aqiuok/xiaozhi-smart-elf/photos/70CE8669092AEE571E4C6250777DF579.jpg

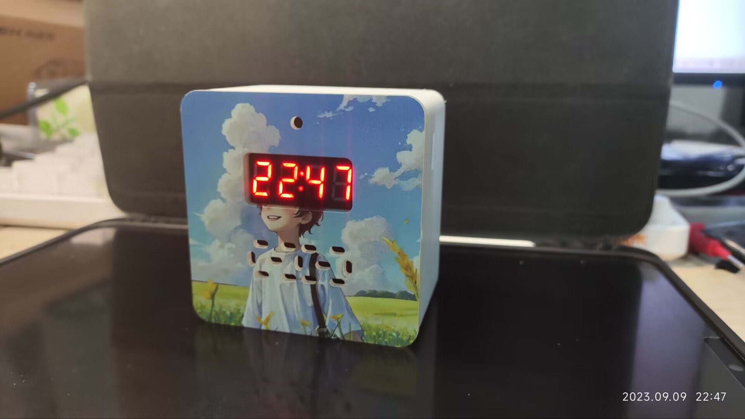
photos/70CE8669092AEE571E4C6250777DF579.jpg
