aqiuok/xiaozhi-smart-elf/photos/Bcm6qwBvF4b9TmoeZIAAMZd9puk0gAqJdHaOMHHB.jpeg

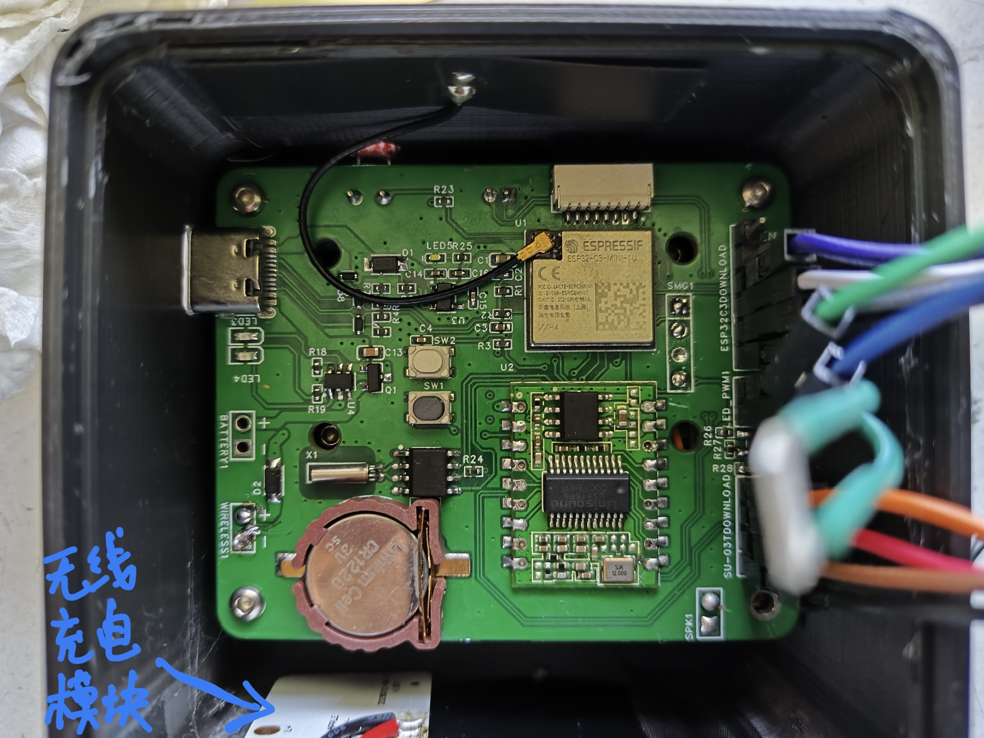
photos/Bcm6qwBvF4b9TmoeZIAAMZd9puk0gAqJdHaOMHHB.jpeg
