aqiuok/xiaozhi-smart-elf/photos/gcC11dQcpo1tZI9Yauk2vhwf6SmNw4uLY4zkg3At.png

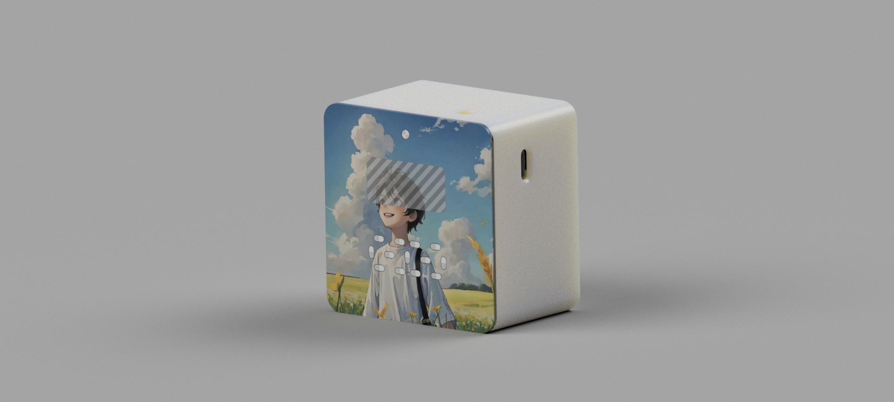
photos/gcC11dQcpo1tZI9Yauk2vhwf6SmNw4uLY4zkg3At.png
