aqiuok/xiaozhi-smart-elf/photos/QQ截图20240616194331.jpg

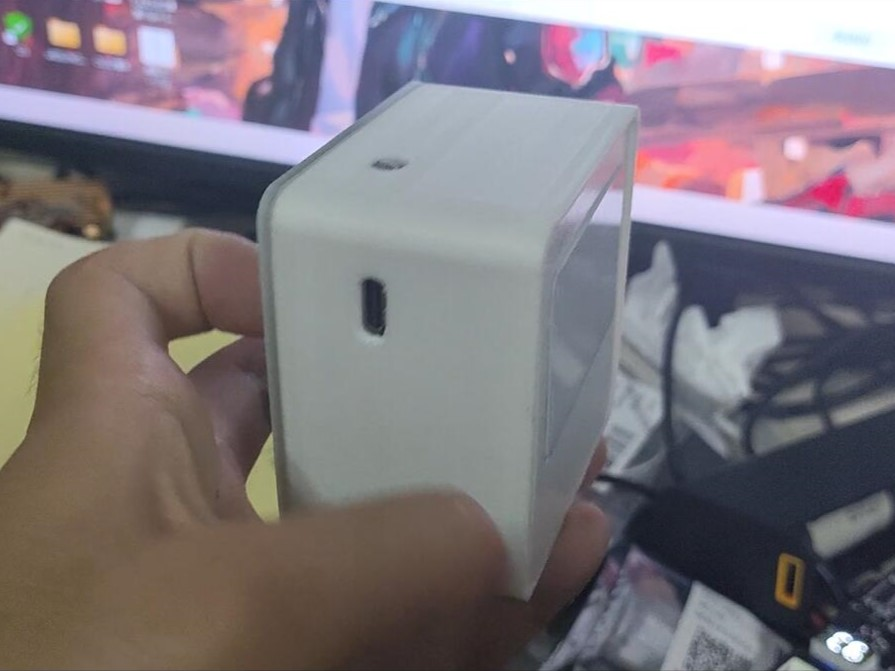
photos/QQ截图20240616194331.jpg
