aqiuok/xiaozhi-smart-elf/photos/前面.jpg

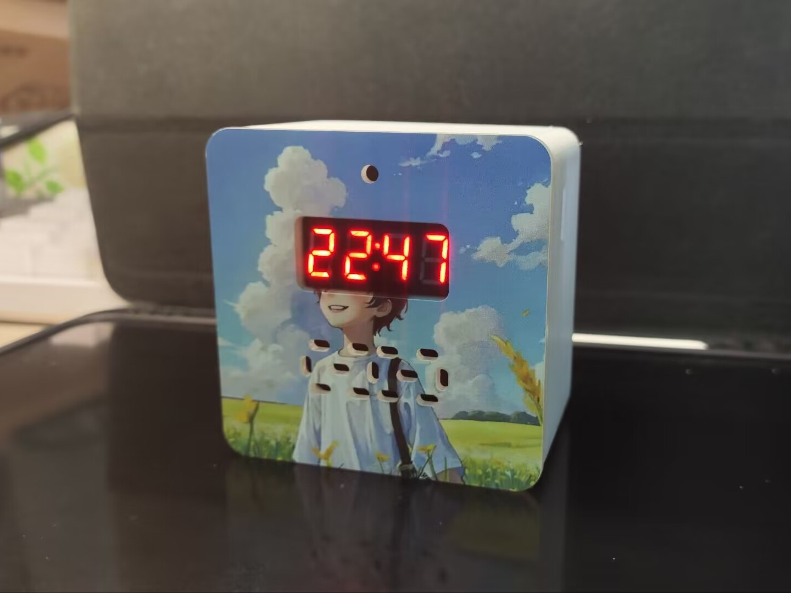
photos/前面.jpg
