aqiuok/xiaozhi-smart-elf/photos/后盖.jpg

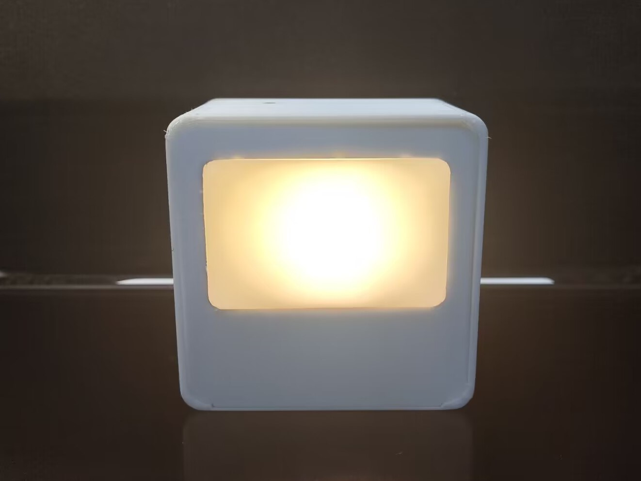
photos/后盖.jpg
